ryan-sondgeroth/FlthyHPs/Maestro/hardware/kicad_libraries/3d_models/d42v55fx-step-down-voltage-regulator.step

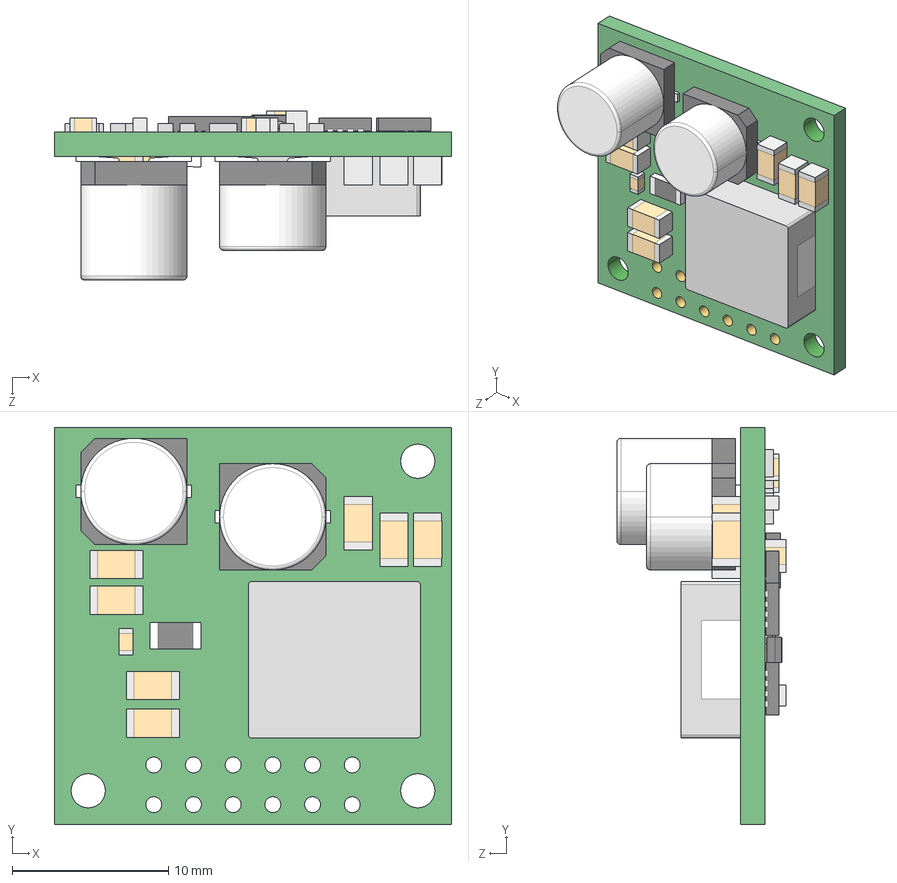
[picture p41: CAD file, 2026-03-27, last stored version]
Maestro/hardware/kicad_libraries/3d_models/d42v55fx-step-down-voltage-regulator.step
25.4 x 25.4 x 10.8 mm
