ryan-sondgeroth/FlthyHPs/Maestro/hardware/kicad_libraries/3d_models/MF-MSMF050-2--3DModel-STEP-56544.STEP

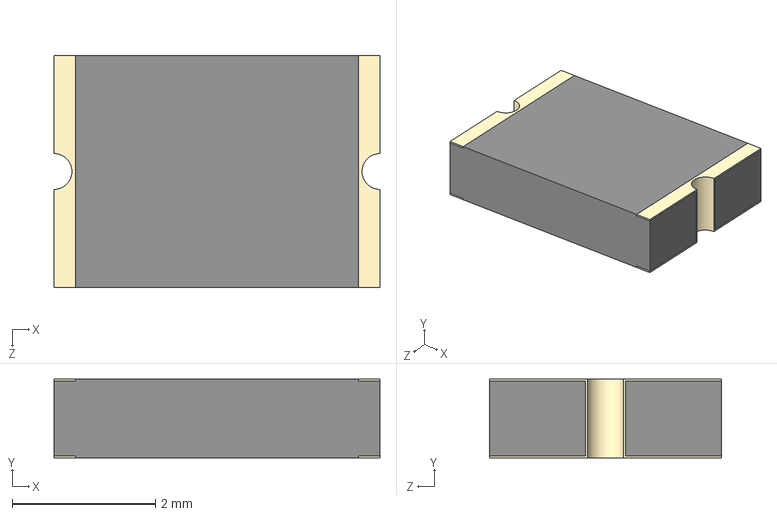
[picture p44: CAD file, 2026-03-27, last stored version]
Maestro/hardware/kicad_libraries/3d_models/MF-MSMF050-2--3DModel-STEP-56544.STEP
4.55 x 1.10 x 3.24 mm
