ryan-sondgeroth/FlthyHPs/Maestro/hardware/kicad_libraries/3d_models/headers/4Pin_Header_Female_2p54mm.step

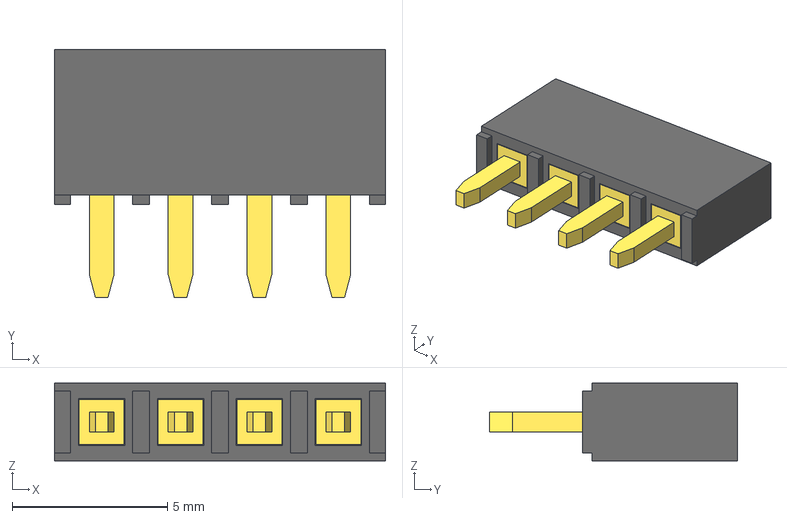
[picture p58: CAD file, 2026-03-27, last stored version]
Maestro/hardware/kicad_libraries/3d_models/headers/4Pin_Header_Female_2p54mm.step
10.7 x 8.00 x 2.50 mm
