ryan-sondgeroth/FlthyHPs/Maestro/hardware/kicad_libraries/3d_models/headers/9Pin_Header_Female_2p54mm.step

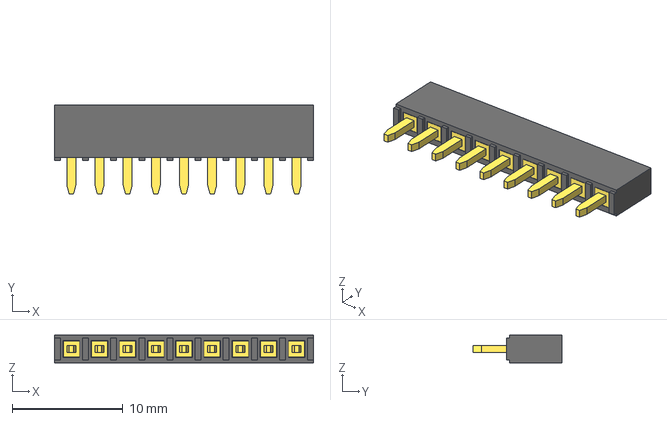
[picture p77: CAD file, 2026-03-27, last stored version]
Maestro/hardware/kicad_libraries/3d_models/headers/9Pin_Header_Female_2p54mm.step
23.4 x 8.00 x 2.50 mm
