ryan-sondgeroth/FlthyHPs/Maestro/hardware/kicad_libraries/3d_models/headers/6Pin_Header_Female_Double_2p54mm.step

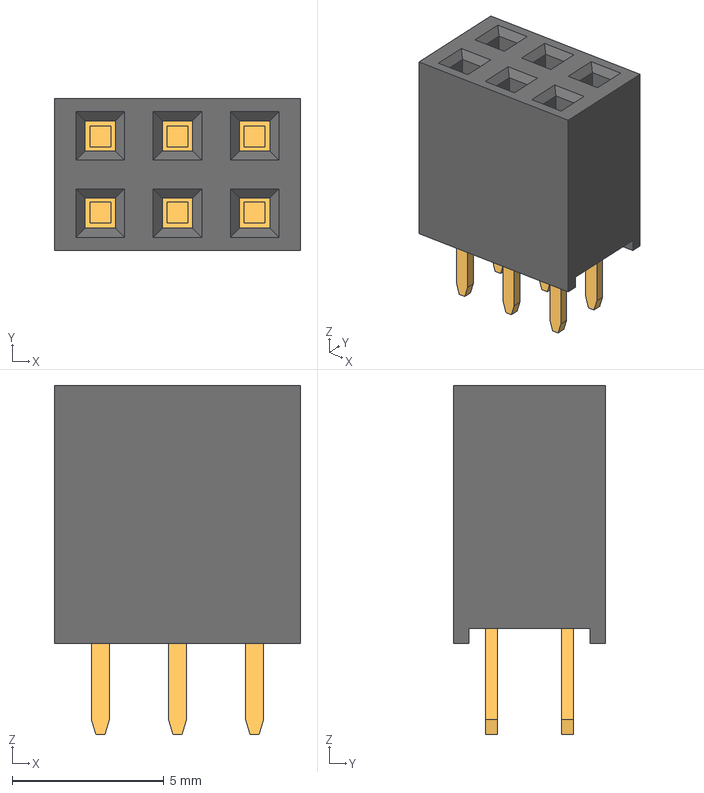
[picture p79: CAD file, 2026-03-27, last stored version]
Maestro/hardware/kicad_libraries/3d_models/headers/6Pin_Header_Female_Double_2p54mm.step
8.12 x 5.00 x 11.5 mm
