ryan-sondgeroth/FlthyHPs/Maestro/hardware/kicad_libraries/3d_models/headers/16Pin_Header_Female_Double_2p54mm.step

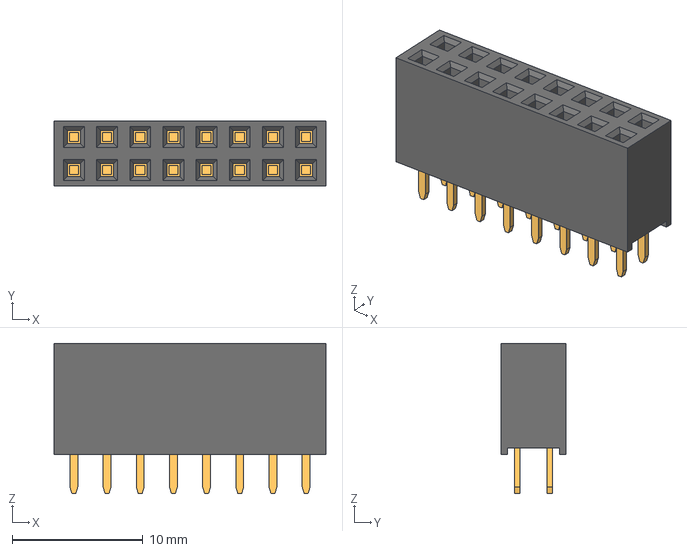
[picture p82: CAD file, 2026-03-27, last stored version]
Maestro/hardware/kicad_libraries/3d_models/headers/16Pin_Header_Female_Double_2p54mm.step
20.8 x 5.00 x 11.5 mm
