ryan-sondgeroth/FlthyHPs/Maestro/hardware/kicad_libraries/3d_models/headers/26Pin_Header_Male_Double_2p54mm.step

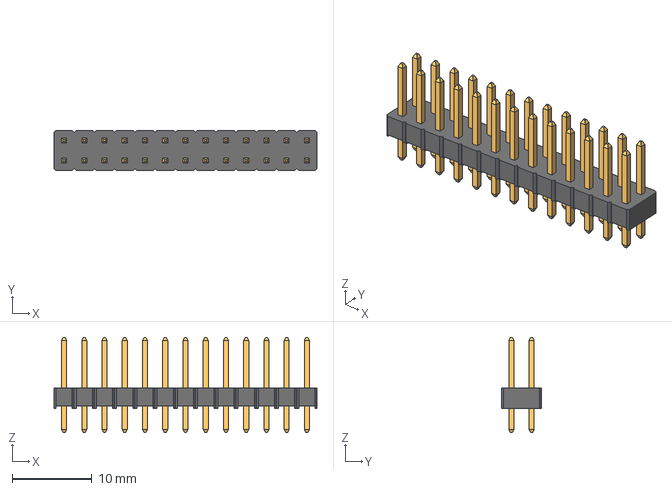
[picture p83: CAD file, 2026-03-27, last stored version]
Maestro/hardware/kicad_libraries/3d_models/headers/26Pin_Header_Male_Double_2p54mm.step
33.0 x 5.08 x 11.9 mm
