ryan-sondgeroth/FlthyHPs/Maestro/hardware/kicad_libraries/3d_models/headers/19Pin_Header_Male_2p54mm.step

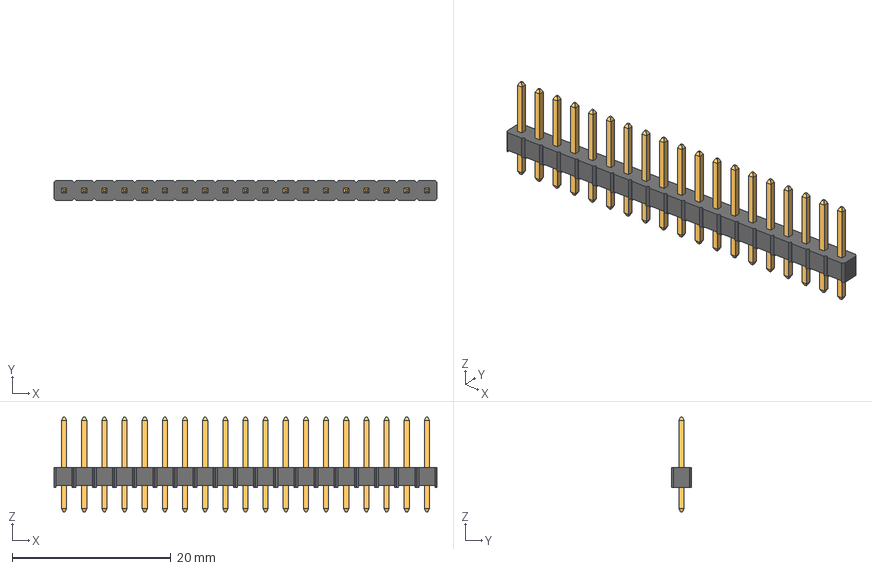
[picture p85: CAD file, 2026-03-27, last stored version]
Maestro/hardware/kicad_libraries/3d_models/headers/19Pin_Header_Male_2p54mm.step
48.3 x 2.54 x 11.9 mm
