ryan-sondgeroth/FlthyHPs/Maestro/hardware/kicad_libraries/3d_models/headers/32Pin_Header_Female_Double_2p54mm.step

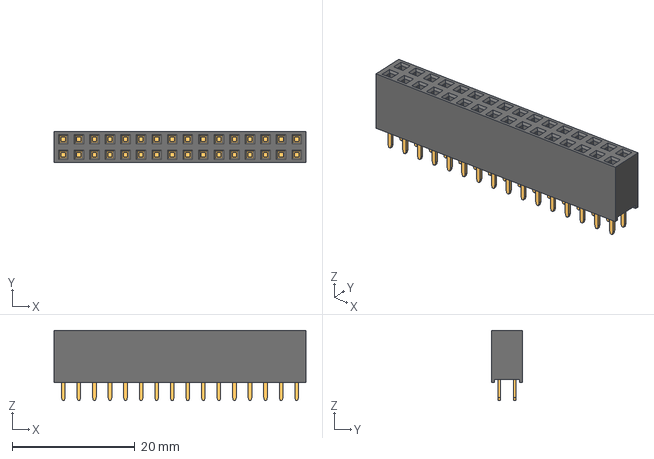
[picture p91: CAD file, 2026-03-27, last stored version]
Maestro/hardware/kicad_libraries/3d_models/headers/32Pin_Header_Female_Double_2p54mm.step
41.1 x 5.00 x 11.5 mm
