ryan-sondgeroth/FlthyHPs/Maestro/hardware/kicad_libraries/3d_models/headers/5Pin_Header_Male_2p54mm.step

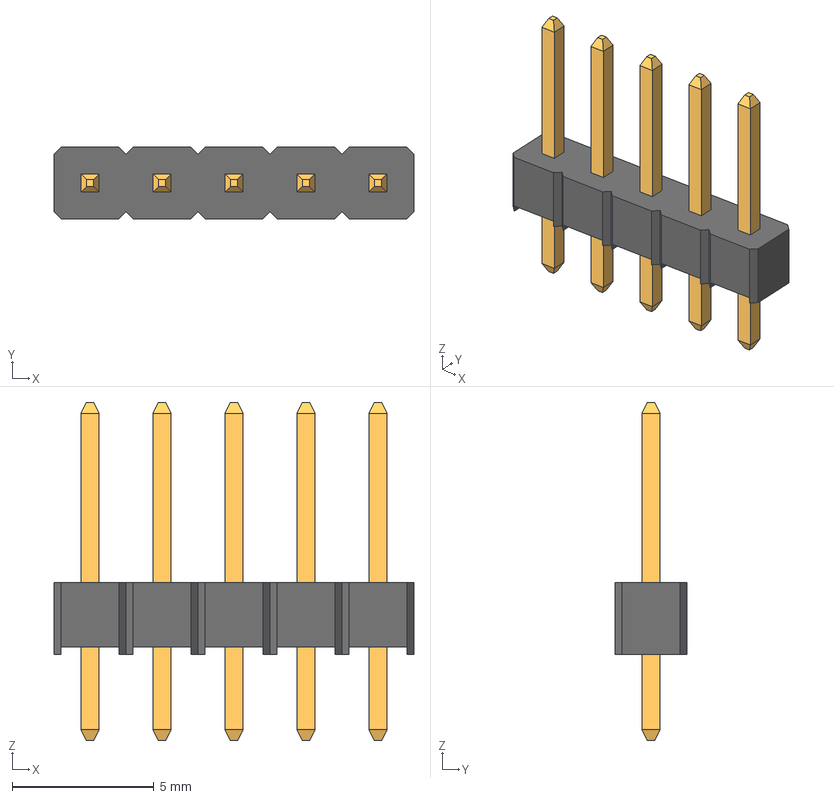
[picture p105: CAD file, 2026-03-27, last stored version]
Maestro/hardware/kicad_libraries/3d_models/headers/5Pin_Header_Male_2p54mm.step
12.7 x 2.54 x 11.9 mm
