ryan-sondgeroth/FlthyHPs/Maestro/hardware/kicad_libraries/3d_models/headers/16Pin_Header_Male_Double_2p54mm.step

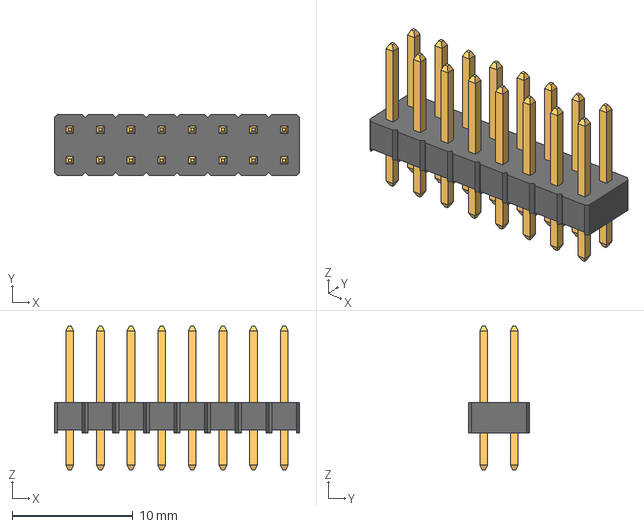
[picture p106: CAD file, 2026-03-27, last stored version]
Maestro/hardware/kicad_libraries/3d_models/headers/16Pin_Header_Male_Double_2p54mm.step
20.3 x 5.08 x 11.9 mm
