ryan-sondgeroth/FlthyHPs/docs/manual_images/image1.png

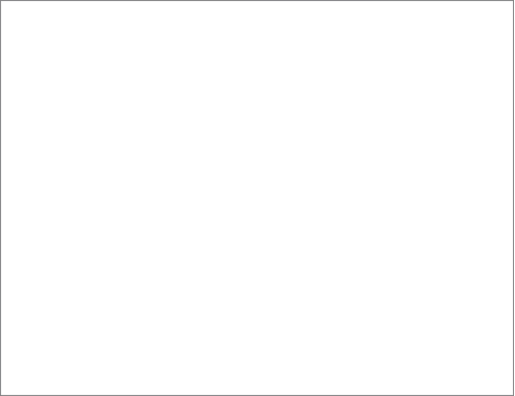
docs/manual_images/image1.png
